LilianJ09/Thermocouple_WiFi/Bank_pictures/Image-1.png

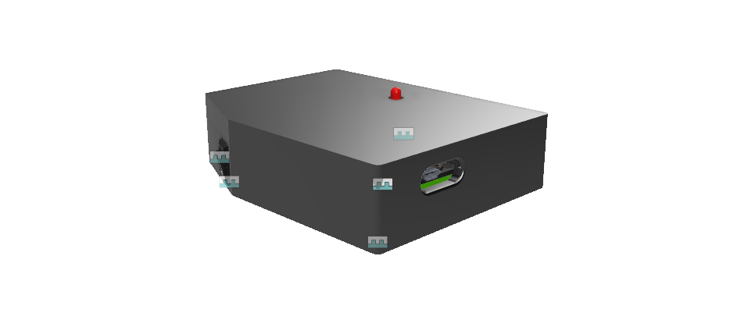
Bank_pictures/Image-1.png
