LilianJ09/Thermocouple_WiFi/Bank_pictures/Image-2.png

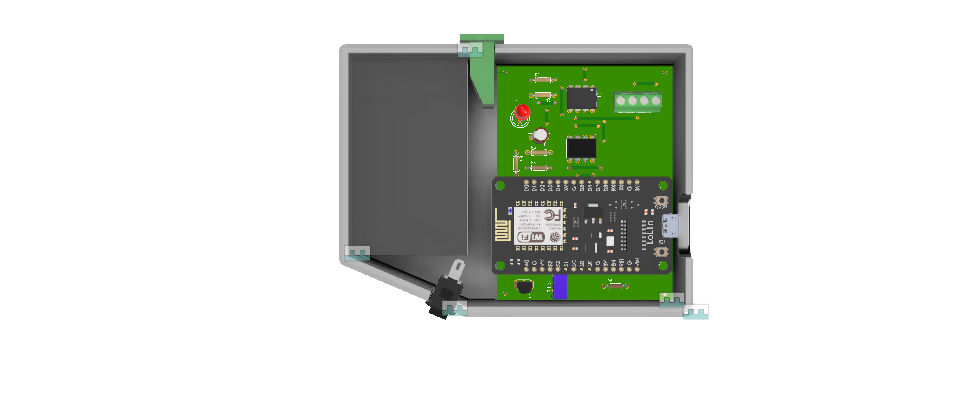
Bank_pictures/Image-2.png
