LilianJ09/Thermocouple_WiFi/Bank_pictures/Image-3.png

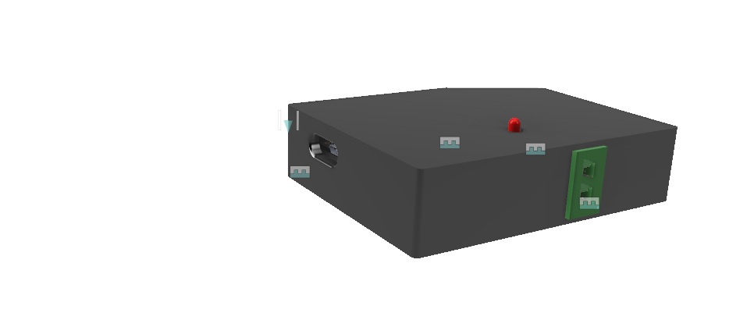
Bank_pictures/Image-3.png
