LilianJ09/Thermocouple_WiFi/Bank_pictures/Image-4.png

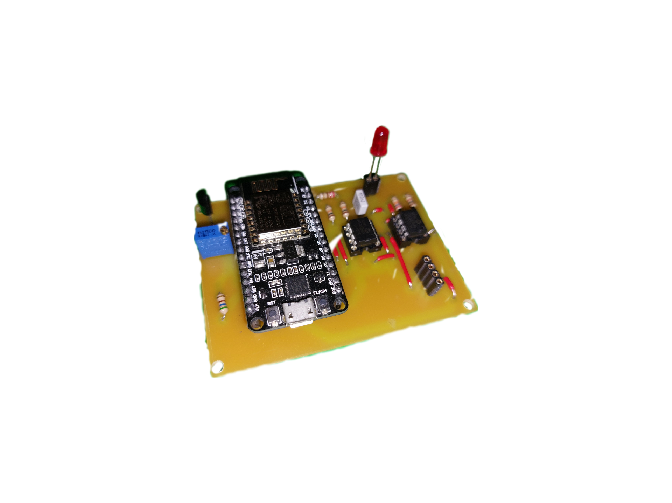
Bank_pictures/Image-4.png
