LilianJ09/Thermocouple_WiFi/Bank_pictures/Image-5.png

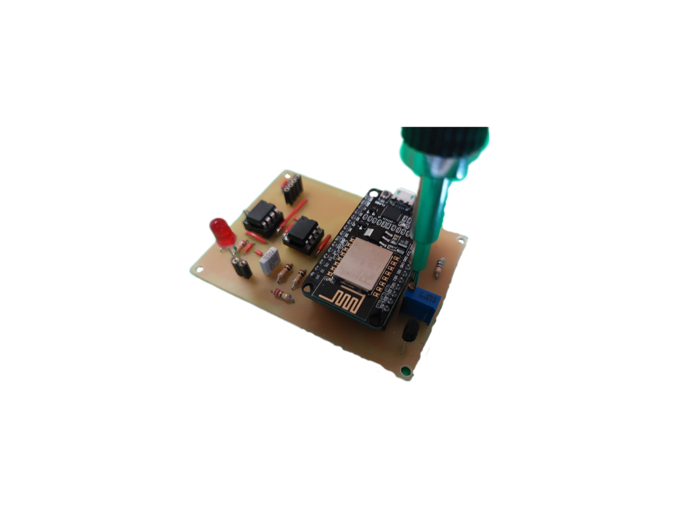
Bank_pictures/Image-5.png
