LilianJ09/Thermocouple_WiFi/Bank_pictures/Image-7.png

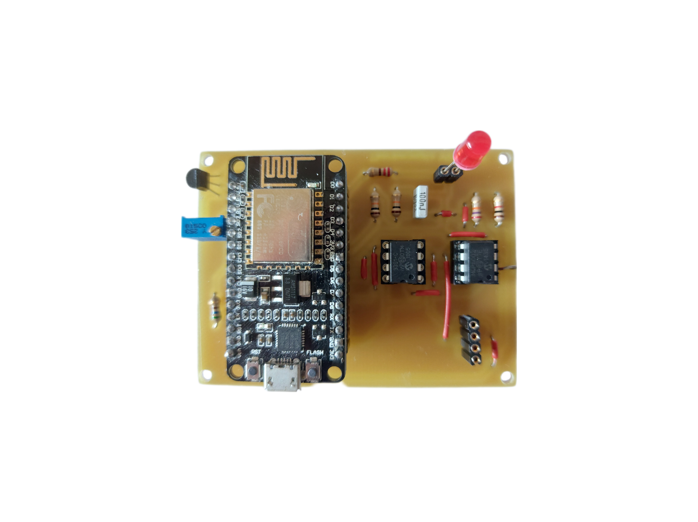
Bank_pictures/Image-7.png
